SeanP2001/Smart_Door_Sensor/Code/Smart_Door_Sensor/SendEmail.cpp

#include "SendEmail.h"

#define SMTP_HOST "smtp.gmail.com"
#define SMTP_PORT 465
// Gmail is port 465 (SSL), less secure apps = enabled. https://myaccount.google.com/lesssecureapps?pli=1

// --------------------------------------------------------------------------- B O T   E M A I L   D E T A I L S ---------------------------------------------------------------------------
#define AUTHOR_NAME "SPUD Smart System"
#define AUTHOR_EMAIL "spudsmartsystem@gmail.com"
#define AUTHOR_PASSWORD "UniProjectEmail2021"

SMTPSession smtp;      // instantiate SMTP object


// ---------------------------------------------------------------------------------- S E N D   E M A I L ----------------------------------------------------------------------------------
void sendEmail(const char* recipientEmail, const char* recipientName, const char* emailSubject, const char* messageText){
  
  smtp.debug(1);

  /* Set the callback function to get the sending results */
  smtp.callback(smtpCallback);

  /* Declare the session config data */
  ESP_Mail_Session session;

  /* Set the session config */
  session.server.host_name = SMTP_HOST;
  session.server.port = SMTP_PORT;
  session.login.email = AUTHOR_EMAIL;
  session.login.password = AUTHOR_PASSWORD;
  session.login.user_domain = "";

  /* Declare the message class */
  SMTP_Message message;

  /* Set the message headers */
  message.sender.name = AUTHOR_NAME;
  message.sender.email = AUTHOR_EMAIL;
  message.subject = emailSubject;
  message.addRecipient(recipientName, recipientEmail);

  /*Send HTML message*/
  /*
  String htmlMsg = "<div style=\"color:#2f4468;\"><h1>Hello World!</h1><p>- Sent from ESP board</p></div>";
  message.html.content = htmlMsg.c_str();
  message.html.content = htmlMsg.c_str();
  message.text.charSet = "us-ascii";
  message.html.transfer_encoding = Content_Transfer_Encoding::enc_7bit;
*/
  
  //Send raw text message
  String textMsg = messageText;
  message.text.content = textMsg.c_str();
/*
  message.text.charSet = "us-ascii";
  message.text.transfer_encoding = Content_Transfer_Encoding::enc_7bit;
  
  message.priority = esp_mail_smtp_priority::esp_mail_smtp_priority_low;
  message.response.notify = esp_mail_smtp_notify_success | esp_mail_smtp_notify_failure | esp_mail_smtp_notify_delay;
*/

  /* Set the custom message header */
  //message.addHeader("Message-ID: <abcde.fghij@gmail.com>");

  /* Connect to server with the session config */
  if (!smtp.connect(&session))
    return;

  /* Start sending Email and close the session */
  if (!MailClient.sendMail(&smtp, &message))
    Serial.println("Error sending Email, " + smtp.errorReason());
}

void smtpCallback(SMTP_Status status){
  /* Print the current status */
  Serial.println(status.info());

  /* Print the sending result */
  if (status.success()){
    Serial.println("----------------");
    ESP_MAIL_PRINTF("Message sent success: %d\n", status.completedCount());
    ESP_MAIL_PRINTF("Message sent failled: %d\n", status.failedCount());
    Serial.println("----------------\n");
    struct tm dt;

    for (size_t i = 0; i < smtp.sendingResult.size(); i++){
      /* Get the result item */
      SMTP_Result result = smtp.sendingResult.getItem(i);
      time_t ts = (time_t)result.timestamp;
      localtime_r(&ts, &dt);

      ESP_MAIL_PRINTF("Message No: %d\n", i + 1);
      ESP_MAIL_PRINTF("Status: %s\n", result.completed ? "success" : "failed");
      ESP_MAIL_PRINTF("Date/Time: %d/%d/%d %d:%d:%d\n", dt.tm_year + 1900, dt.tm_mon + 1, dt.tm_mday, dt.tm_hour, dt.tm_min, dt.tm_sec);
      ESP_MAIL_PRINTF("Recipient: %s\n", result.recipients);
      ESP_MAIL_PRINTF("Subject: %s\n", result.subject);
    }
    Serial.println("----------------\n");
  }
}
